natanoj/heatcontrol/pcb/roomunit-display-midas.top.png

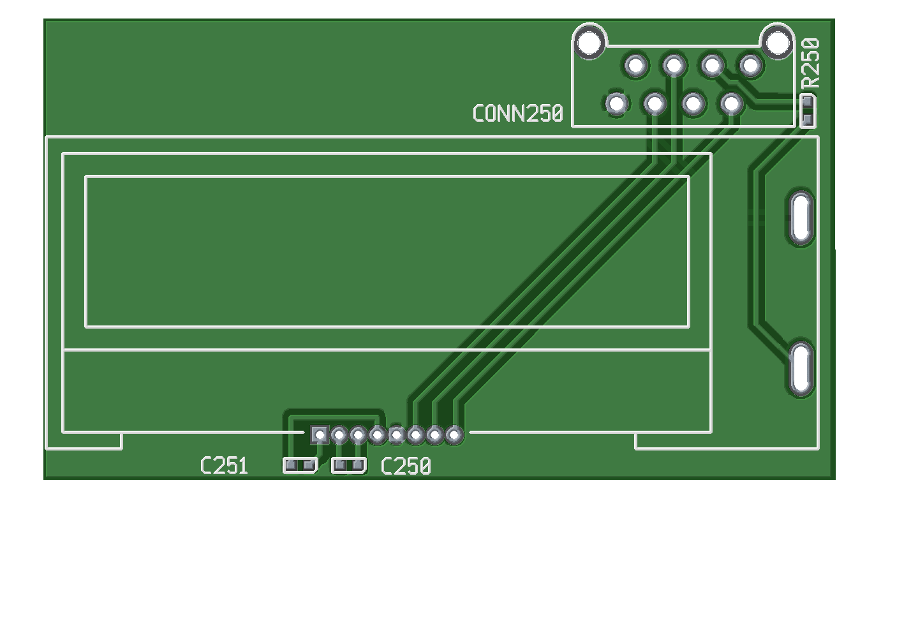
pcb/roomunit-display-midas.top.png
