natanoj/heatcontrol/pcb/roomunit-psu.bottom.png

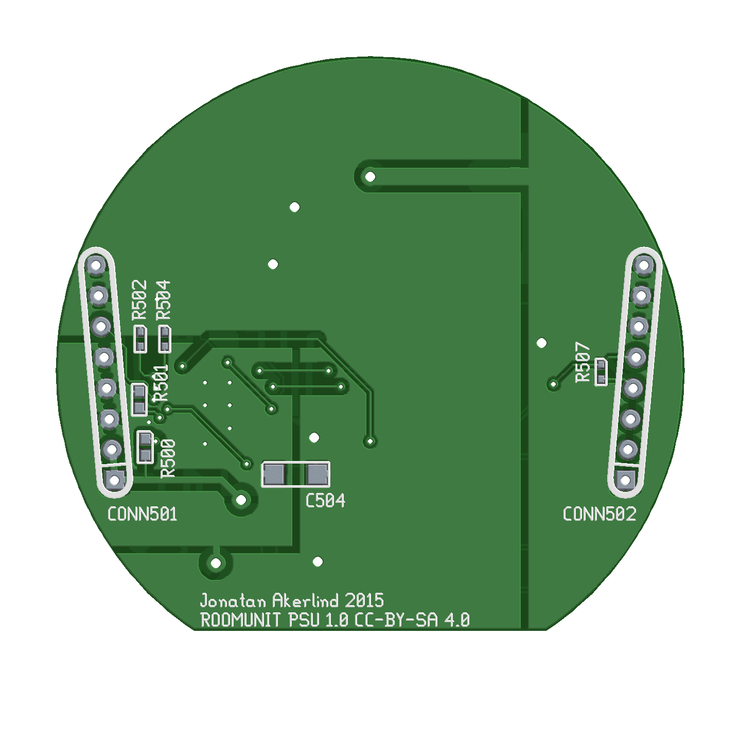
pcb/roomunit-psu.bottom.png
